CheAhMeD/Theia/DesktopApp/screenshots/tool.png

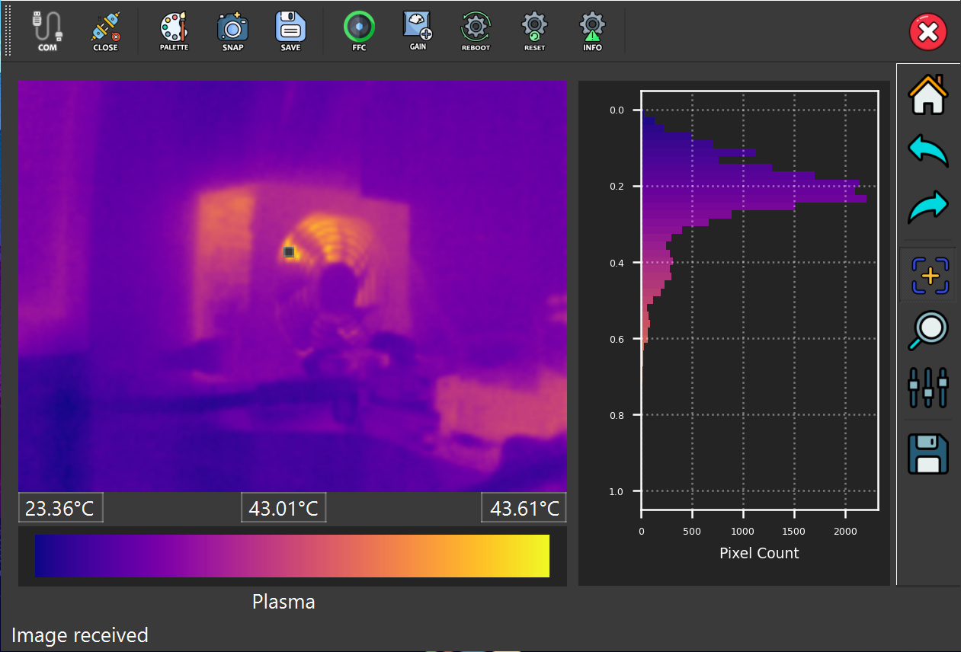
DesktopApp/screenshots/tool.png
