CheAhMeD/Theia/images/IMG_2426.jpeg

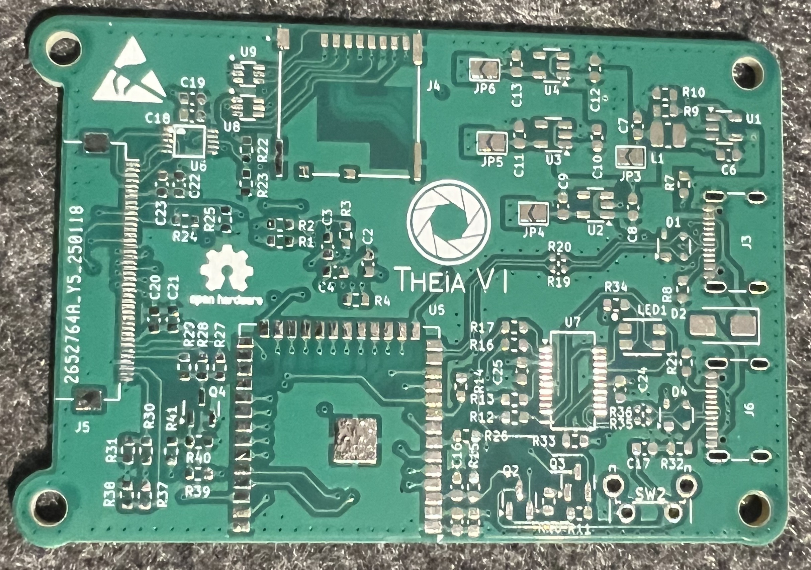
images/IMG_2426.jpeg
