CheAhMeD/Theia/Samples/IMG_1.bmp

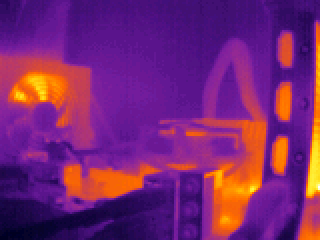
Samples/IMG_1.bmp
