CheAhMeD/Theia/Samples/IMG_2.bmp

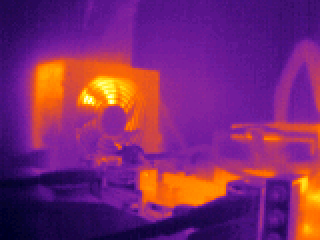
Samples/IMG_2.bmp
