CheAhMeD/Theia/Samples/IMG_7.bmp

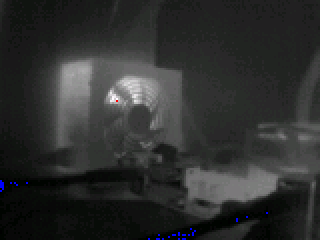
Samples/IMG_7.bmp
