CheAhMeD/Theia/Samples/IMG_12.bmp

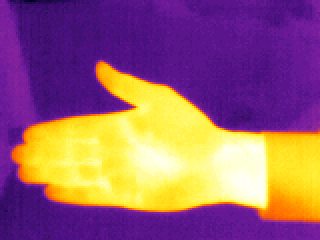
Samples/IMG_12.bmp
