CheAhMeD/Theia/Samples/IMG_13.bmp

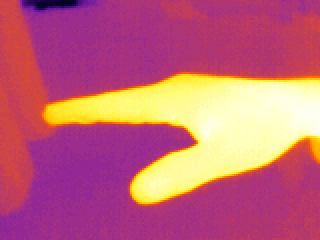
Samples/IMG_13.bmp
