CheAhMeD/Theia/Samples/IMG_14.bmp

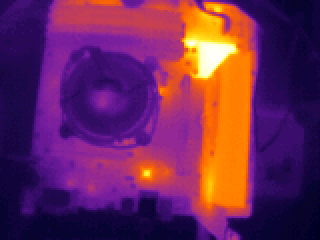
Samples/IMG_14.bmp
