CheAhMeD/Theia/Firmware/theia_v1/arctic.h

/*
 * "Artic" colormap for 8-bit LEP indexed data
 *
 * Copyright 2020 Dan Julio
 *
 * This file is part of tCam.
 *
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
 */
#ifndef PALETTE_ARCTIC_H
#define PALETTE_ARCTIC_H

#include "vars.h"

palette_map_t arctic_palette_map = {
	{15,16,146},
	{15,16,146},
	{15,15,153},
	{15,15,153},
	{15,15,159},
	{15,15,159},
	{16,15,167},
	{16,15,167},
	{15,15,175},
	{15,15,175},
	{16,15,182},
	{16,15,182},
	{16,16,190},
	{16,16,190},
	{14,15,197},
	{14,15,197},
	{15,15,205},
	{15,15,205},
	{15,15,211},
	{15,15,211},
	{16,15,219},
	{16,15,219},
	{16,15,227},
	{16,15,227},
	{16,18,239},
	{16,18,239},
	{16,25,240},
	{16,25,240},
	{15,34,239},
	{15,34,239},
	{15,44,238},
	{15,44,238},
	{14,54,239},
	{14,54,239},
	{14,63,239},
	{14,63,239},
	{14,74,238},
	{14,74,238},
	{17,82,238},
	{17,82,238},
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
};

#endif
