CheAhMeD/Theia/Firmware/theia_v1/banded.h

/*
 * Banded colormap for 8-bit LEP indexed data
 *
 * Copyright 2021 Dan Julio
 *
 * This file is part of firecam.
 *
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
 */
#ifndef PALETTE_BANDED_H
#define PALETTE_BANDED_H

#include "vars.h"

palette_map_t banded_palette_map = {
	{0,0,0},
	{0,0,0},
	{0,0,0},
	{0,0,0},
	{0,0,0},
	{0,0,0},
	{0,0,0},
	{0,0,0},
	{0,0,0},
	{0,0,0},
	{0,0,0},
	{0,0,0},
	{0,0,0},
	{96,0,80},
	{96,0,80},
	{96,0,80},
	{96,0,80},
	{96,0,80},
	{96,0,80},
	{96,0,80},
	{96,0,80},
	{96,0,80},
	{96,0,80},
	{96,0,80},
	{96,0,80},
	{96,0,80},
	{48,48,80},
	{48,48,80},
	{48,48,80},
	{48,48,80},
	{48,48,80},
	{48,48,80},
	{48,48,80},
	{48,48,80},
	{48,48,80},
	{48,48,80},
	{48,48,80},
	{48,48,80},
	{48,48,80},
	{48,48,112},
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
};

#endif
