CheAhMeD/Theia/Firmware/theia_v1/blackhot.h

/*
 * Inverse grayscale colormap for 8-bit LEP indexed data
 *
 * Copyright 2021 Dan Julio
 *
 * This file is part of tCam.
 *
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
 */
#ifndef PALETTE_BLACKHOT_H
#define PALETTE_BLACKHOT_H

#include "vars.h"

palette_map_t blackhot_palette_map = {
	{255,255,255},
	{254,254,254},
	{253,253,253},
	{252,252,252},
	{251,251,251},
	{250,250,250},
	{249,249,249},
	{248,248,248},
	{247,247,247},
	{246,246,246},
	{245,245,245},
	{244,244,244},
	{243,243,243},
	{242,242,242},
	{241,241,241},
	{240,240,240},
	{239,239,239},
	{238,238,238},
	{237,237,237},
	{236,236,236},
	{235,235,235},
	{234,234,234},
	{233,233,233},
	{232,232,232},
	{231,231,231},
	{230,230,230},
	{229,229,229},
	{228,228,228},
	{227,227,227},
	{226,226,226},
	{225,225,225},
	{224,224,224},
	{223,223,223},
	{222,222,222},
	{221,221,221},
	{220,220,220},
	{219,219,219},
	{218,218,218},
	{217,217,217},
	{216,216,216},
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
};

#endif
