CheAhMeD/Theia/Firmware/theia_v1/double_rainbow.h

/*
 * "Double rainbow" colormap for 8-bit LEP indexed data
 *
 * Copyright 2020 Dan Julio
 *
 * This file is part of tCam.
 *
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
 */
#ifndef PALETTE_DOUBLE_RAINBOW_H
#define PALETTE_DOUBLE_RAINBOW_H

#include "vars.h"

palette_map_t double_rainbow_palette_map = {
	{18,15,18},
	{25,17,26},
	{34,18,32},
	{43,19,39},
	{52,21,48},
	{60,23,55},
	{69,25,62},
	{77,26,70},
	{86,28,75},
	{95,30,84},
	{103,31,91},
	{112,34,98},
	{120,35,106},
	{129,36,111},
	{138,39,120},
	{146,40,128},
	{155,42,136},
	{150,44,140},
	{145,47,146},
	{139,51,151},
	{134,54,157},
	{130,57,161},
	{124,60,168},
	{119,63,172},
	{115,66,179},
	{109,70,183},
	{104,73,189},
	{99,76,194},
	{93,80,200},
	{89,83,205},
	{84,86,211},
	{78,90,216},
	{73,92,222},
	{69,96,227},
	{63,99,233},
	{59,103,238},
	{57,104,230},
	{54,107,221},
	{50,109,213},
	{50,113,206},
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
};

#endif
