CheAhMeD/Theia/Firmware/theia_v1/fusion.h

/*
 * "Fusion" colormap for 8-bit LEP indexed data
 *
 * Copyright 2020 Dan Julio
 *
 * This file is part of tCam.
 *
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
 */
#ifndef PALETTE_FUSION_H
#define PALETTE_FUSION_H

#include "vars.h"

palette_map_t fusion_palette_map = {
	{0,2,36},
	{1,2,37},
	{3,3,38},
	{3,3,39},
	{5,3,41},
	{6,3,42},
	{8,4,44},
	{8,4,46},
	{10,4,47},
	{12,5,49},
	{14,5,51},
	{15,5,53},
	{17,6,56},
	{18,6,58},
	{20,7,61},
	{22,6,62},
	{24,7,66},
	{26,7,68},
	{28,8,70},
	{30,8,73},
	{32,9,75},
	{35,9,78},
	{36,9,81},
	{39,10,84},
	{41,10,86},
	{43,11,89},
	{46,11,91},
	{47,11,95},
	{50,13,97},
	{52,13,101},
	{55,13,103},
	{57,13,106},
	{59,14,109},
	{61,14,111},
	{64,16,114},
	{66,16,116},
	{68,16,119},
	{71,16,121},
	{74,18,123},
	{76,18,127},
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
};

#endif
