CheAhMeD/Theia/Firmware/theia_v1/gray.h

/*
 * Grayscale colormap for 8-bit LEP indexed data
 *
 * Copyright 2020 Dan Julio
 *
 * This file is part of tCam.
 *
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
 */
#ifndef PALETTE_GRAY_H
#define PALETTE_GRAY_H

#include "vars.h"

palette_map_t gray_palette_map = {
	{0,0,0},
	{1,1,1},
	{2,2,2},
	{3,3,3},
	{4,4,4},
	{5,5,5},
	{6,6,6},
	{7,7,7},
	{8,8,8},
	{9,9,9},
	{10,10,10},
	{11,11,11},
	{12,12,12},
	{13,13,13},
	{14,14,14},
	{15,15,15},
	{16,16,16},
	{17,17,17},
	{18,18,18},
	{19,19,19},
	{20,20,20},
	{21,21,21},
	{22,22,22},
	{23,23,23},
	{24,24,24},
	{25,25,25},
	{26,26,26},
	{27,27,27},
	{28,28,28},
	{29,29,29},
	{30,30,30},
	{31,31,31},
	{32,32,32},
	{33,33,33},
	{34,34,34},
	{35,35,35},
	{36,36,36},
	{37,37,37},
	{38,38,38},
	{39,39,39},
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
};

#endif
