CheAhMeD/Theia/Firmware/theia_v1/ice.h

#ifndef PALETTE_ICE_H
#define PALETTE_ICE_H

#include "vars.h"
palette_map_t ice_palette_map = {
 {0, 0, 0},
 {0, 1, 2},
 {0, 1, 4},
 {0, 3, 6},
 {0, 4, 7},
 {0, 5, 10},
 {0, 6, 11},
 {0, 7, 13},
 {0, 8, 15},
 {0, 9, 16},
 {0, 10, 19},
 {0, 11, 21},
 {1, 12, 22},
 {1, 13, 24},
 {1, 13, 25},
 {1, 14, 28},
 {1, 15, 30},
 {0, 16, 32},
 {1, 17, 33},
 {1, 18, 35},
 {1, 19, 36},
 {1, 20, 39},
 {1, 21, 41},
 {2, 21, 42},
 {1, 23, 44},
 {2, 23, 46},
 {2, 25, 47},
 {2, 26, 50},
 {2, 27, 52},
 {1, 28, 53},
 {2, 29, 55},
 {2, 30, 56},
 {2, 31, 59},
 {2, 32, 61},
 {2, 32, 63},
 {2, 33, 64},
 {3, 34, 66},
 {3, 35, 67},
 {3, 36, 70},
 {3, 37, 71},
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
};

#endif
