CheAhMeD/Theia/Firmware/theia_v1/ironblack.h

/*
 * "Ironblack" colormap for 8-bit LEP indexed data
 *
 * Copyright 2020 Dan Julio
 *
 * This file is part of firecam.
 *
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
 */
#ifndef PALETTE_IRONBLACK_H
#define PALETTE_IRONBLACK_H

#include "vars.h"

palette_map_t ironblack_palette_map = {
	{255,255,255},
	{253,253,253},
	{251,251,251},
	{249,249,249},
	{247,247,247},
	{245,245,245},
	{243,243,243},
	{241,241,241},
	{239,239,239},
	{237,237,237},
	{235,235,235},
	{233,233,233},
	{231,231,231},
	{229,229,229},
	{227,227,227},
	{225,225,225},
	{223,223,223},
	{221,221,221},
	{219,219,219},
	{217,217,217},
	{215,215,215},
	{213,213,213},
	{211,211,211},
	{209,209,209},
	{207,207,207},
	{205,205,205},
	{203,203,203},
	{201,201,201},
	{199,199,199},
	{197,197,197},
	{195,195,195},
	{193,193,193},
	{191,191,191},
	{189,189,189},
	{187,187,187},
	{185,185,185},
	{183,183,183},
	{181,181,181},
	{179,179,179},
	{177,177,177},
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
};

#endif /* IRONBLACK */
