CheAhMeD/Theia/Firmware/theia_v1/rainbow.h

/*
 * "Rainbow" colormap for 8-bit LEP indexed data
 *
 * Copyright 2020 Dan Julio
 *
 * This file is part of firecam.
 *
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
 */
#ifndef PALETTE_RAINBOW_H
#define PALETTE_RAINBOW_H

#include "vars.h"

palette_map_t rainbow_palette_map = {
	{1,3,74},
	{0,3,74},
	{0,3,75},
	{0,3,75},
	{0,3,76},
	{0,3,76},
	{0,3,77},
	{0,3,79},
	{0,3,82},
	{0,5,85},
	{0,7,88},
	{0,10,91},
	{0,14,94},
	{0,19,98},
	{0,22,100},
	{0,25,103},
	{0,28,106},
	{0,32,109},
	{0,35,112},
	{0,38,116},
	{0,40,119},
	{0,42,123},
	{0,45,128},
	{0,49,133},
	{0,50,134},
	{0,51,136},
	{0,52,137},
	{0,53,139},
	{0,54,142},
	{0,55,144},
	{0,56,145},
	{0,58,149},
	{0,61,154},
	{0,63,156},
	{0,65,159},
	{0,66,161},
	{0,68,164},
	{0,69,167},
	{0,71,170},
	{0,73,174},
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
};

#endif /* PALETTE_RAINBOW_H */
