CheAhMeD/Theia/Firmware/theia_v1/sepia.h

/*
 * "Sepia" colormap for 8-bit LEP indexed data
 *
 * Copyright 2021 Dan Julio
 *
 * This file is part of tCam.
 *
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
 */
#ifndef PALETTE_SEPIA_H
#define PALETTE_SEPIA_H

#include "vars.h"

palette_map_t sepia_palette_map = {
	{0,0,0},
	{1,1,1},
	{3,2,1},
	{4,3,2},
	{6,4,2},
	{7,5,3},
	{8,6,3},
	{10,7,4},
	{11,8,4},
	{13,9,5},
	{14,11,5},
	{15,12,6},
	{17,13,6},
	{18,14,7},
	{20,15,7},
	{21,16,8},
	{22,17,8},
	{24,18,9},
	{25,19,9},
	{27,20,10},
	{28,21,10},
	{29,22,11},
	{31,23,11},
	{32,24,12},
	{34,25,12},
	{35,26,13},
	{36,27,13},
	{38,28,14},
	{39,29,14},
	{41,30,15},
	{42,32,15},
	{43,33,16},
	{45,34,16},
	{46,35,17},
	{48,36,17},
	{49,37,18},
	{50,38,18},
	{52,39,19},
	{53,40,19},
	{55,41,20},
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
};

#endif
