CheAhMeD/Theia/Firmware/theia_v1/ui.c

#if defined(EEZ_FOR_LVGL)
#include <eez/core/vars.h>
#endif

#include "ui.h"
#include "screens.h"
#include "actions.h"
#include "vars.h"

#if defined(EEZ_FOR_LVGL)

void ui_init() {
    eez_flow_init(assets, sizeof(assets), (lv_obj_t **)&objects, sizeof(objects), images, sizeof(images), actions);
}

void ui_tick() {
    eez_flow_tick();
    tick_screen(g_currentScreen);
}

#else

#include <string.h>

static int16_t currentScreen = -1;

static lv_obj_t *getLvglObjectFromIndex(int32_t index) {
    if (index == -1) {
        return 0;
    }
    return ((lv_obj_t **)&objects)[index];
}

void loadScreen(enum ScreensEnum screenId) {
    currentScreen = screenId - 1;
    lv_obj_t *screen = getLvglObjectFromIndex(currentScreen);
    lv_scr_load(screen);
}

void ui_init() {
    create_screens();
    set_var_act_scr_id(SCREEN_ID_MAIN_SCREEN);
    clear_lepton_image();
    clear_browse_image();
    loadScreen(SCREEN_ID_MAIN_SCREEN);
}

void ui_tick() {
    tick_screen(currentScreen);
}

#endif
